Fredrik-Reinholdsen/kallisto/src/master/src/key_map.rs

use kallisto_components::keyboard::types::*;

pub const N_KEYS: usize = 42;
pub const BASE_LAYER: [Option<LayerKeyMap>; N_KEYS] = [
    // Left half, Row 1
    Some(LayerKeyMap {
        pressed: Some(KeyMapping {
            key: KeyPress::CapsLock,
            modifier: None,
        }),
        held_press: None,
    }),
    Some(LayerKeyMap {
        pressed: Some(KeyMapping {
            key: KeyPress::Q,
            modifier: None,
        }),
        held_press: None,
    }),
    Some(LayerKeyMap {
        pressed: Some(KeyMapping {
            key: KeyPress::W,
            modifier: None,
        }),
        held_press: None,
    }),
    Some(LayerKeyMap {
        pressed: Some(KeyMapping {
            key: KeyPress::E,
            modifier: None,
        }),
        held_press: None,
    }),
    Some(LayerKeyMap {
        pressed: Some(KeyMapping {
            key: KeyPress::R,
            modifier: None,
        }),
        held_press: None,
    }),
    Some(LayerKeyMap {
        pressed: Some(KeyMapping {
            key: KeyPress::T,
            modifier: None,
        }),
        held_press: None,
    }),
    Some(LayerKeyMap {
        pressed: Some(KeyMapping {
            key: KeyPress::Space,
            modifier: None,
        }),
        held_press: None,
    }),
    // Left half, Row 2
    Some(LayerKeyMap {
        pressed: Some(KeyMapping {
            key: KeyPress::Tab,
            modifier: None,
        }),
        held_press: None,
    }),
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
            modifier: None,
        }),
        held_press: None,
    }),
    Some(LayerKeyMap {
        pressed: Some(KeyMapping {
            key: KeyPress::F11,
            modifier: None,
        }),
        held_press: None,
    }),
    // Right half, Row 2
    None,
    Some(LayerKeyMap {
        pressed: Some(KeyMapping {
            key: KeyPress::Keyboard6,
            modifier: None,
        }),
        held_press: None,
    }),
    Some(LayerKeyMap {
        pressed: Some(KeyMapping {
            key: KeyPress::Keyboard7,
            modifier: None,
        }),
        held_press: None,
    }),
    Some(LayerKeyMap {
        pressed: Some(KeyMapping {
            key: KeyPress::Keyboard8,
            modifier: None,
        }),
        held_press: None,
    }),
    Some(LayerKeyMap {
        pressed: Some(KeyMapping {
            key: KeyPress::Keyboard9,
            modifier: None,
        }),
        held_press: None,
    }),
    Some(LayerKeyMap {
        pressed: Some(KeyMapping {
            key: KeyPress::Keyboard0,
            modifier: None,
        }),
        held_press: None,
    }),
    None,
    // Right half, Row 3
    None,
    None,
    None,
    None,
    None,
    None,
    None,
];
